overthemax/AtmoVerse2.0/tests/EInk_Display_HW_Test/EInk_Display_HW_Test.ino

/*
  Minimal test sketch for the GxEPD2 5.83" e-ink display (GDEW0583T8) on ESP32
  - Wire the pins as in the defines below
  - Open the Serial Monitor at 115200 baud
*/

#include <GxEPD2_BW.h>
#include <SPI.h>

// === PINS ===
#define EPD_BUSY    4    // GPIO04 - busy
#define EPD_RST     16   // GPIO16 - res (reset)
#define EPD_DC      17   // GPIO17 - d/c (data/command)
#define EPD_CS      5    // GPIO05 - cs (chip select)
#define EPD_SCK     18   // GPIO18 - sck (clock)
#define EPD_MOSI    23   // GPIO23 - sdi (data in/MOSI)

// === DISPLAY OBJECT ===
GxEPD2_BW<GxEPD2_583_T8, GxEPD2_583_T8::HEIGHT> display(GxEPD2_583_T8(EPD_CS, EPD_DC, EPD_RST, EPD_BUSY));

void setup() {
  Serial.begin(115200);
  delay(500);
  Serial.println("\n===== E-INK DISPLAY TEST 5.83\" =====");

  // SPI for the display
  SPI.begin(EPD_SCK, -1, EPD_MOSI, EPD_CS);

  display.init(115200);
  display.setRotation(0);
  display.setTextColor(GxEPD_BLACK);
  display.setFullWindow();
  Serial.println("Display ready");

  // Test screen
  display.firstPage();
  do {
    display.fillScreen(GxEPD_WHITE);
    display.setFont(NULL);
    display.setCursor(10, 60);
    display.print("TEST E-INK");
    display.setCursor(10, 120);
    display.print("AtmoVerse 2.0");
    display.setCursor(10, 180);
    display.print("OK!");
  } while (display.nextPage());
  Serial.println("Test done. If you see the text, the display works.");
}

void loop() {
}
